IM-TechieScientist/librelab/firmware/src/platform/platform.c

/**
 * @file platform.c
 * @brief Pico platform hardware initialization implementation
 *
 * This file initializes the platform services used by the RP2350 firmware.
 */

#include <stdint.h>

#include "hardware/clocks.h"
#include "hardware/watchdog.h"
#include "pico/stdlib.h"

#include "platform/internal_adc_frontend.h"
#include "platform.h"

void PLATFORM_init(void)
{
    /* Pico SDK runtime performs the core clock/runtime setup before main(). */
    internal_adc_frontend_register();
}

uint32_t PLATFORM_get_tick(void)
{
    return to_ms_since_boot(get_absolute_time());
}

uint64_t PLATFORM_get_time_us(void)
{
    return to_us_since_boot(get_absolute_time());
}

uint32_t PLATFORM_get_peripheral_clock_speed(PLATFORM_PeripheralClock clock)
{
    if (clock == PLATFORM_CLOCK_INVALID) {
        return 0;
    }

    return clock_get_hz(clk_sys);
}

void PLATFORM_idle(void)
{
    tight_loop_contents();
}

__attribute__((noreturn)) void PLATFORM_reset(void)
{
    watchdog_reboot(0, 0, 0);

    for (;;) {
        tight_loop_contents();
    }
}
