IM-TechieScientist/librelab/firmware/esp_firmware/main/mdns_service.h

#ifndef MDNS_SERVICE_H
#define MDNS_SERVICE_H

#include <stdbool.h>
#include <stdint.h>

/*
 * Publishes the LibreLab Pico bridge as librelab-pico.local and exposes its
 * TCP SCPI endpoint through the _librelab._tcp service.
 *
 * Call this after the station interface has received an IP address.
 */
bool mdns_service_start(uint16_t scpi_port);

#endif
